mneuhaus/wonky/docs/native-bridge/proposal-resident.md

# Native bridge proposal: native-resident bodies behind a narrow session API

Date: 2026-09-22. Bend 2.0.25, Apple M5 Pro (18 logical CPUs), macOS arm64, Node v22.23.1.
Role: architecture proposal. It combines the four measurement reports in this folder
([profile](profile.md), [surface](surface.md), [binding](binding.md), [baseline](baseline.md)) with three small new
measurements (section 17). It builds no kernel and claims no speedup that was not measured. Every end-to-end number
below is an **arithmetic projection** from measured parts, generated by `scripts/native-bridge/resident-projection.mjs`.
All inputs were measured on a shared machine at load average 11.6 to 15.2 on 18 cores, so they are indicative.

## 0. Verdict

1. **In-process embedding works, so this design builds on it.** The binding stage ran Bend-emitted C inside Node as a
   plain N-API addon: 0.5 µs per empty call, bit-exact with the JS target, and as fast as a standalone native
   binary. It also proved **heap residency on the real kernel**: `subtract` kept its result in the Bend heap, that
   body fed `union` directly, and the result was bit-exact with the JS chain (`kernel-t1.json`, `chain`). The
   out-of-process service costs 22 to 29 µs per call and 26 ms per MB. It stays an optional isolation layer, not the
   binding.
2. **Residency is not a speed feature, and this proposal does not sell it as one.** The native chain and the same
   chain routed through JS differ by less than 1 % (1521 vs 1501 to 1513 ms). Marshaling costs under 1.5 ms per heavy
   operation. The speed comes from two other sources, and neither depends on residency:
   - native execution: k = 8.3 to 9.7 at 1 thread and 12.8 to 15.3 at 6 threads on the four measured planar Boolean
     calls;
   - not loading the Bend-compiled JS kernel: 745 to 806 ms per CLI run.
3. **What residency buys:**
   - **Exactness by construction.** `nativeChainExact: false` goes away because nothing is decoded and re-encoded
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
