mneuhaus/wonky/fixtures/fillet/onshape/fp22/fp22c.stl

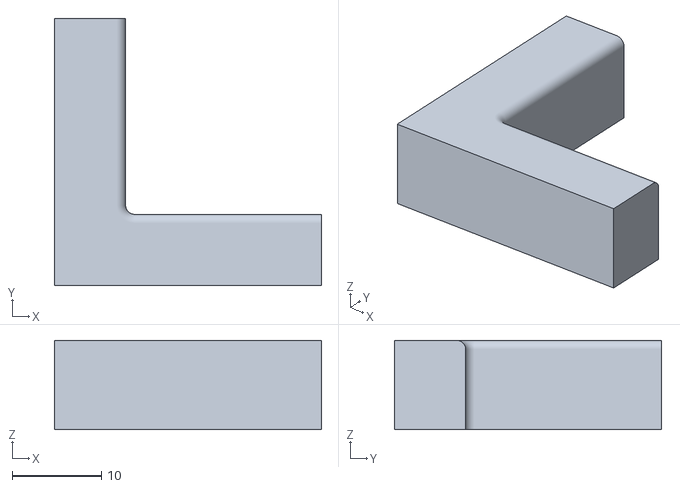
[picture p15: CAD file, 2026-09-27]
fixtures/fillet/onshape/fp22/fp22c.stl
30.0 x 30.0 x 10.0
