mneuhaus/wonky/fixtures/step-regression/periodic-pcurves/model.step

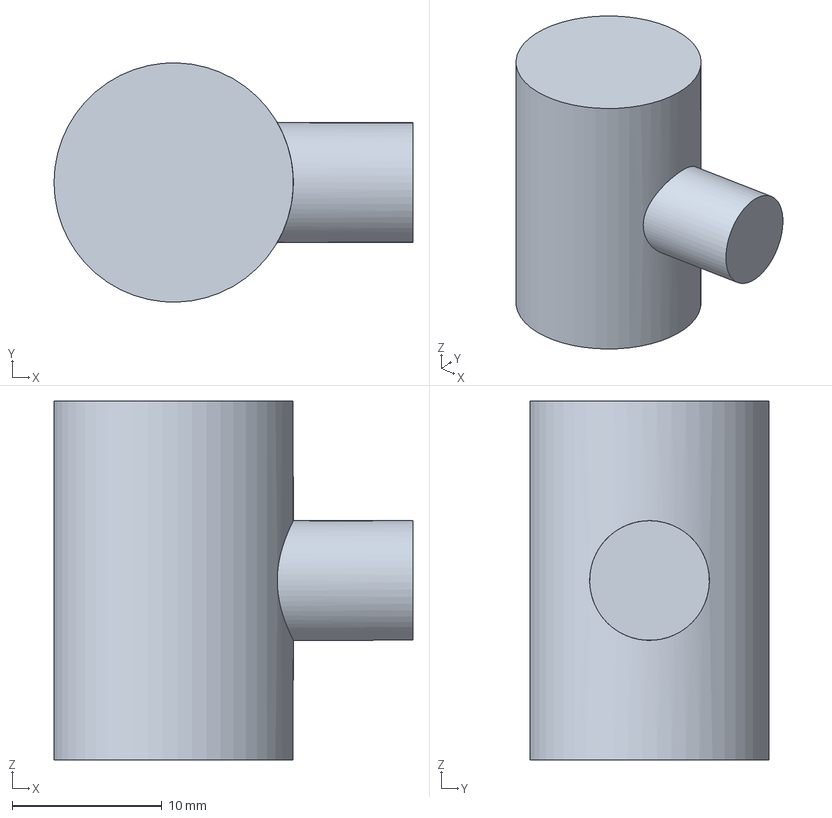
[picture p16: CAD file, 2026-10-04]
fixtures/step-regression/periodic-pcurves/model.step
24.0 x 16.0 x 24.0 mm
