mneuhaus/wonky/fixtures/fillet/onshape/fp17/fp17c.stl

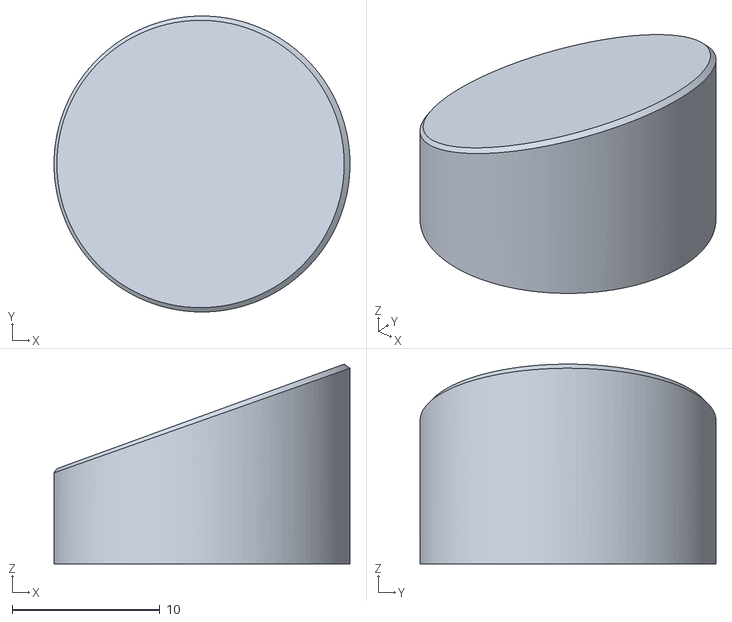
[picture p17: CAD file, 2026-09-27]
fixtures/fillet/onshape/fp17/fp17c.stl
20.0 x 20.0 x 13.5
