mneuhaus/wonky/fixtures/fillet/onshape/fp18/fp18c.stl

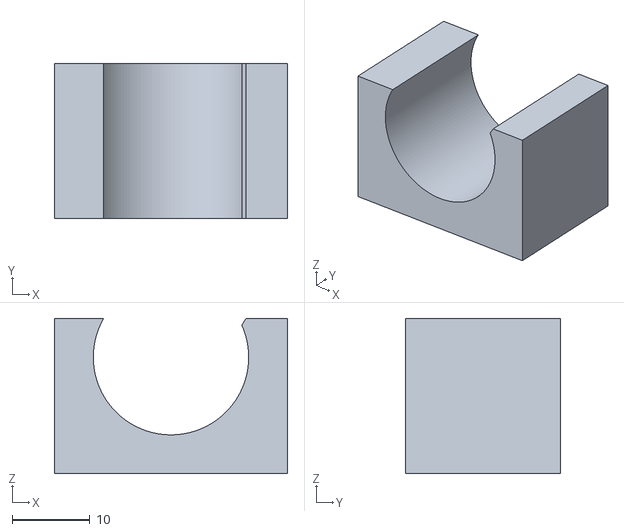
[picture p18: CAD file, 2026-09-27]
fixtures/fillet/onshape/fp18/fp18c.stl
30.0 x 20.0 x 20.0
