mneuhaus/wonky/fixtures/fillet/onshape/fp21/fp21a.stl

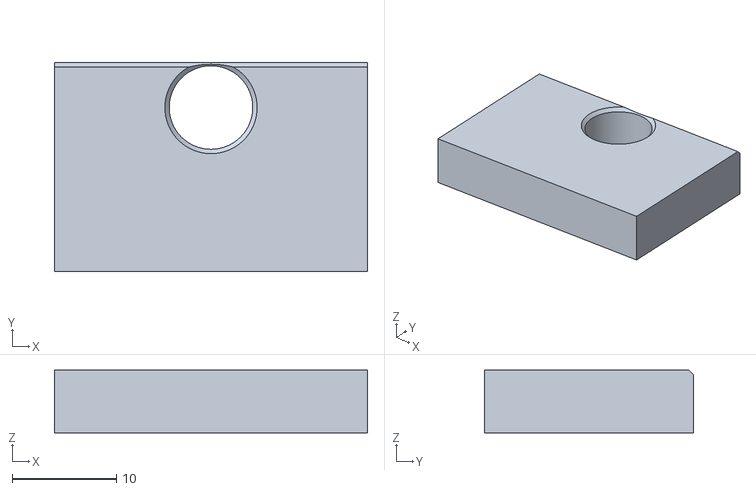
[picture p19: CAD file, 2026-09-27]
fixtures/fillet/onshape/fp21/fp21a.stl
30.0 x 20.0 x 6.00
