mneuhaus/wonky/fixtures/rust/occt-oracle/exports/boolean-overlap-union.step

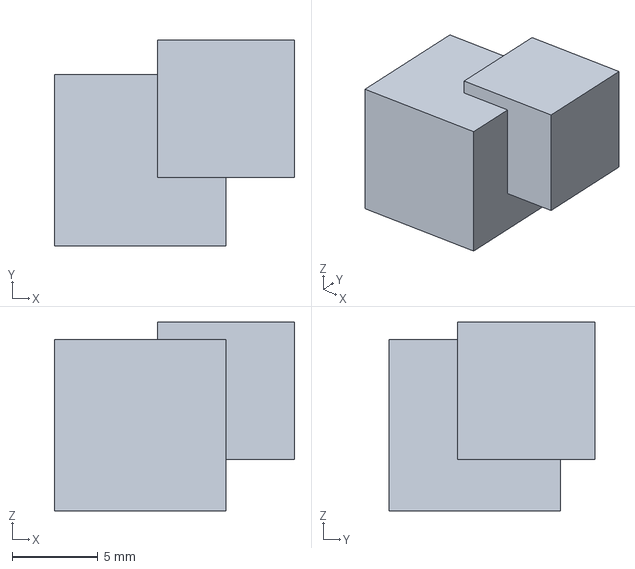
[picture p20: CAD file, 2026-09-27]
fixtures/rust/occt-oracle/exports/boolean-overlap-union.step
14.0 x 12.0 x 11.0 mm
