mneuhaus/wonky/fixtures/fillet/onshape/fp17/fp17b.stl

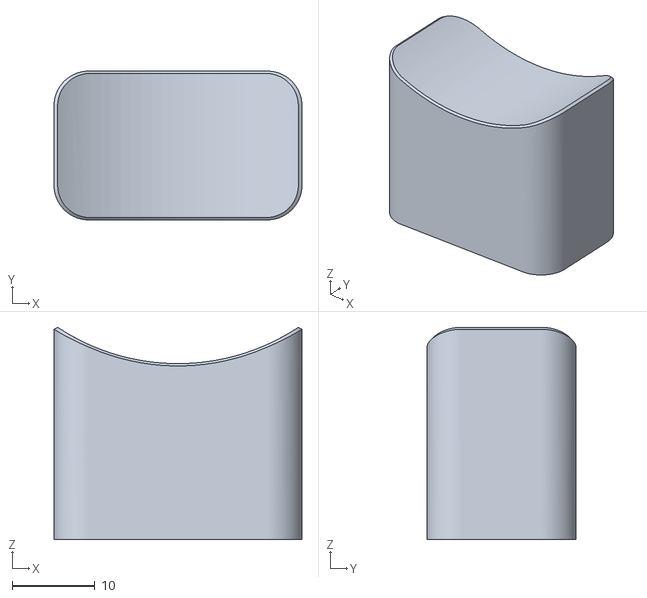
[picture p21: CAD file, 2026-09-27]
fixtures/fillet/onshape/fp17/fp17b.stl
30.0 x 18.0 x 25.7
