mneuhaus/wonky/fixtures/fillet/onshape/fp18/fp18a.stl

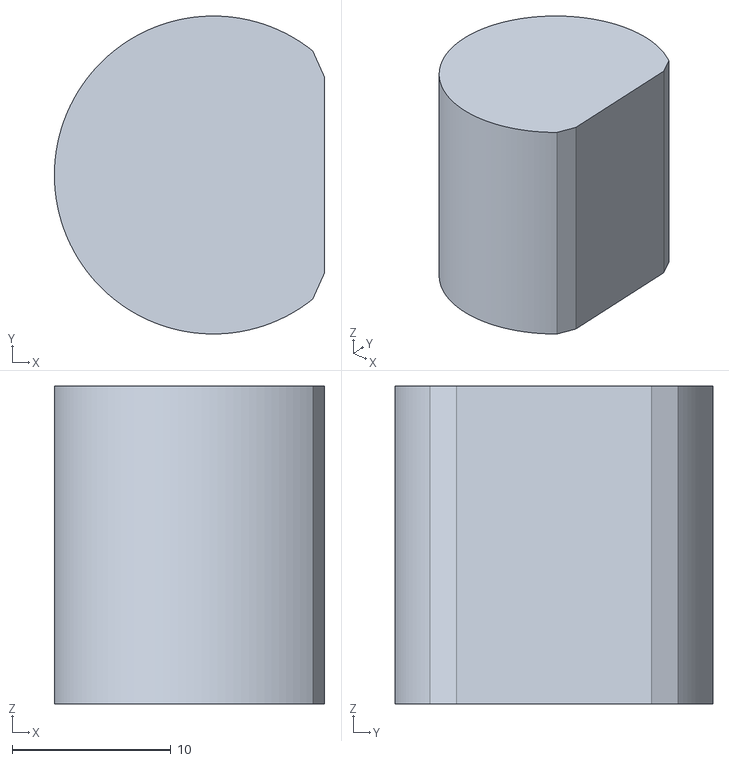
[picture p22: CAD file, 2026-09-27]
fixtures/fillet/onshape/fp18/fp18a.stl
17.0 x 20.0 x 20.0
