mneuhaus/wonky/fixtures/rust/occt-oracle/exports/boolean-sphere-near-tangent-contained-intersect.step

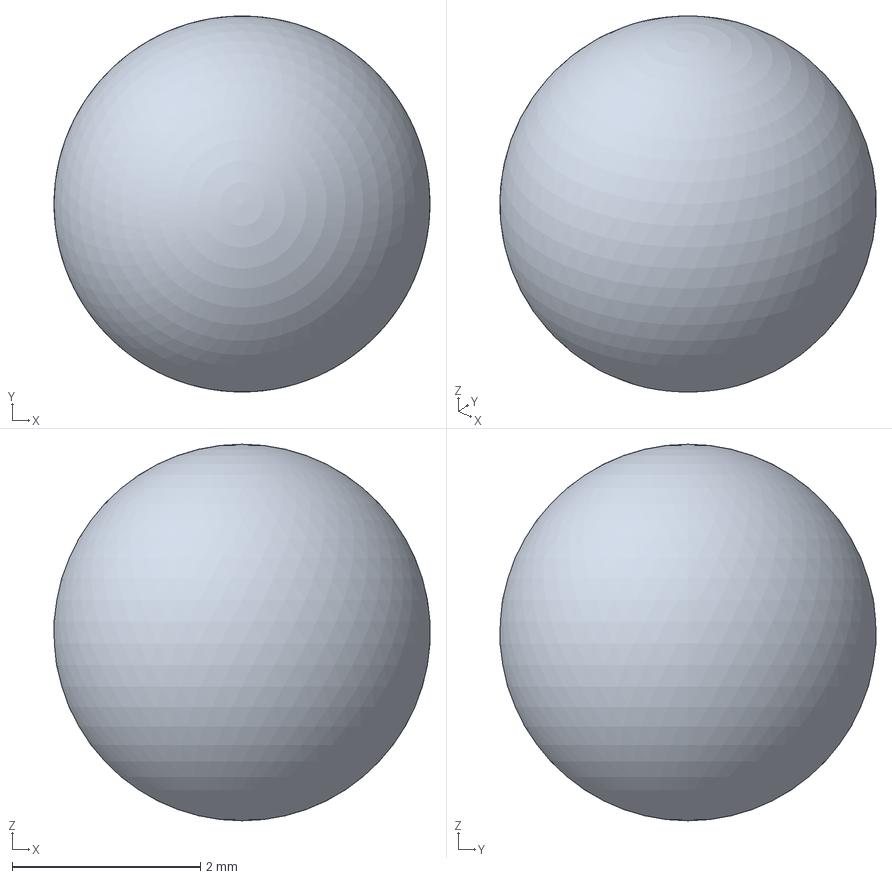
[picture p23: CAD file, 2026-09-27]
fixtures/rust/occt-oracle/exports/boolean-sphere-near-tangent-contained-intersect.step
3.99 x 3.99 x 4.00 mm
