mneuhaus/wonky/fixtures/rust/occt-oracle/exports/primitive-box.step

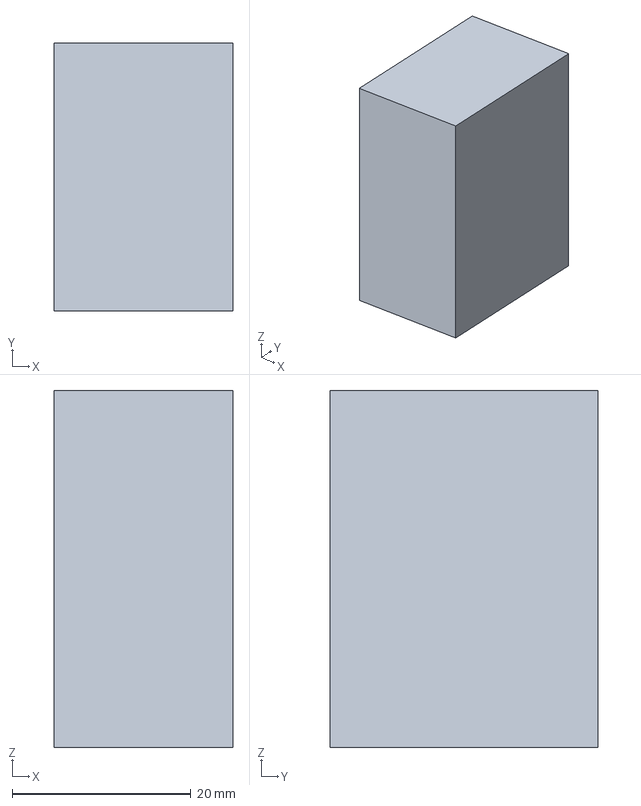
[picture p24: CAD file, 2026-09-27]
fixtures/rust/occt-oracle/exports/primitive-box.step
20.0 x 30.0 x 40.0 mm
