mneuhaus/wonky/fixtures/rust/occt-oracle/exports/boolean-sphere-internal-tangent-subtract.step

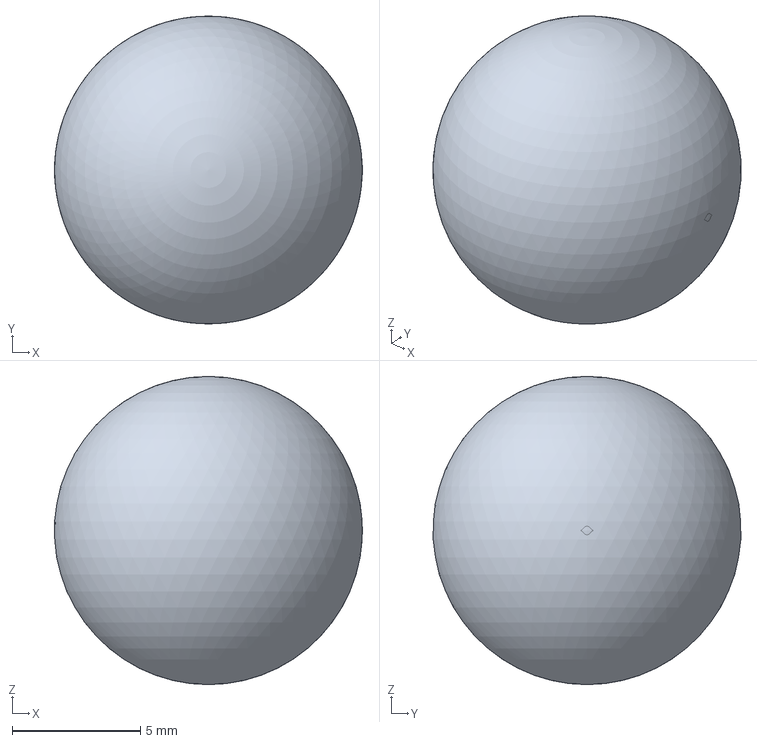
[picture p25: CAD file, 2026-09-27]
fixtures/rust/occt-oracle/exports/boolean-sphere-internal-tangent-subtract.step
12.0 x 12.0 x 12.0 mm
