mneuhaus/wonky/fixtures/rust/occt-oracle/exports/primitive-sphere.step

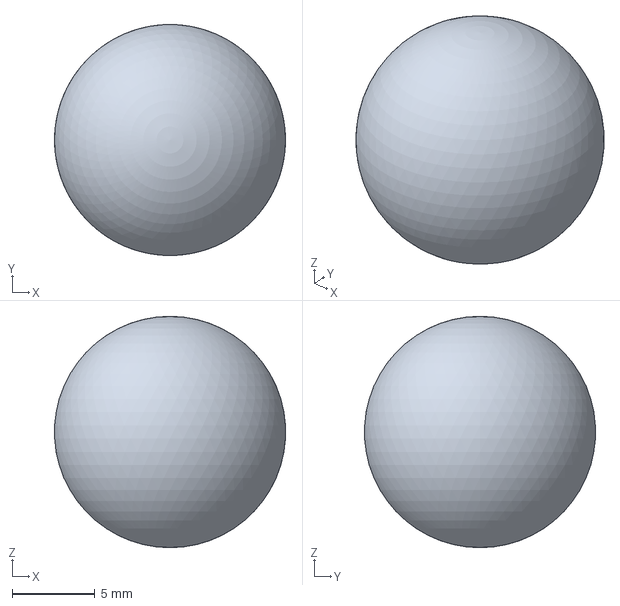
[picture p26: CAD file, 2026-09-27]
fixtures/rust/occt-oracle/exports/primitive-sphere.step
14.0 x 14.0 x 14.0 mm
