mneuhaus/wonky/fixtures/rust/occt-oracle/exports/primitive-cone.step

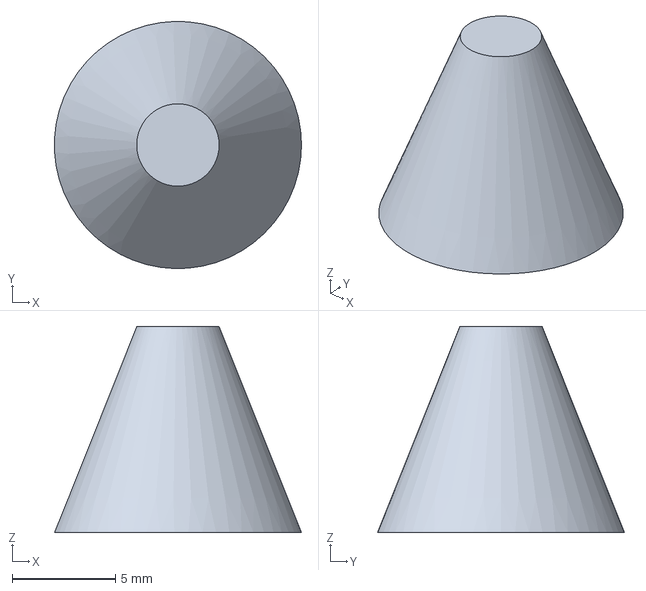
[picture p27: CAD file, 2026-09-27]
fixtures/rust/occt-oracle/exports/primitive-cone.step
12.0 x 12.0 x 10.0 mm
