mneuhaus/wonky/fixtures/rust/occt-oracle/exports/fillet-box-all-edges-r1_5.step

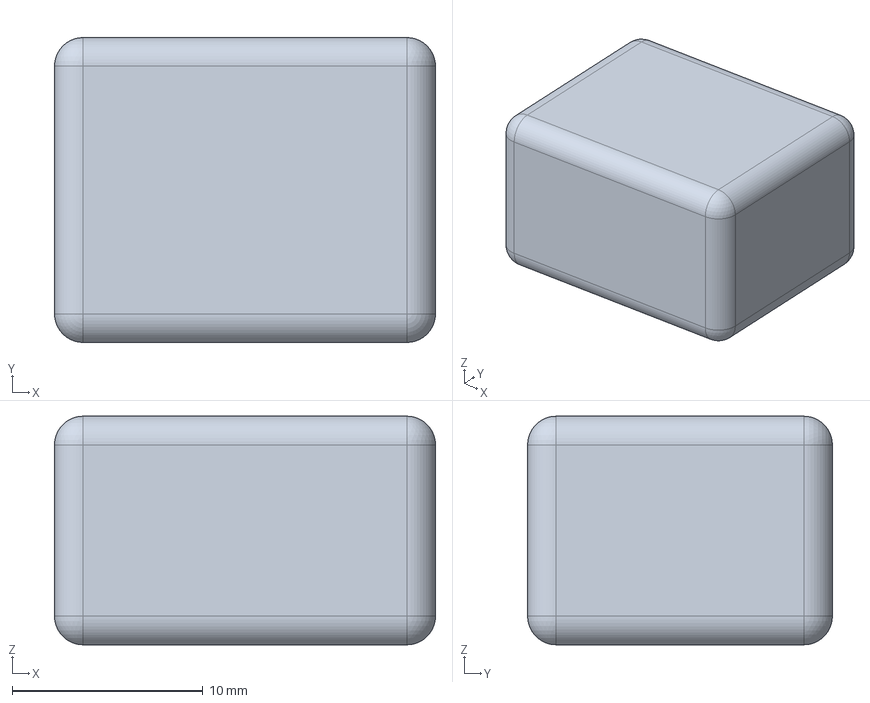
[picture p28: CAD file, 2026-09-27]
fixtures/rust/occt-oracle/exports/fillet-box-all-edges-r1_5.step
20.0 x 16.0 x 12.0 mm
