mneuhaus/wonky/fixtures/rust/occt-oracle/exports/boolean-overlap-subtract.step

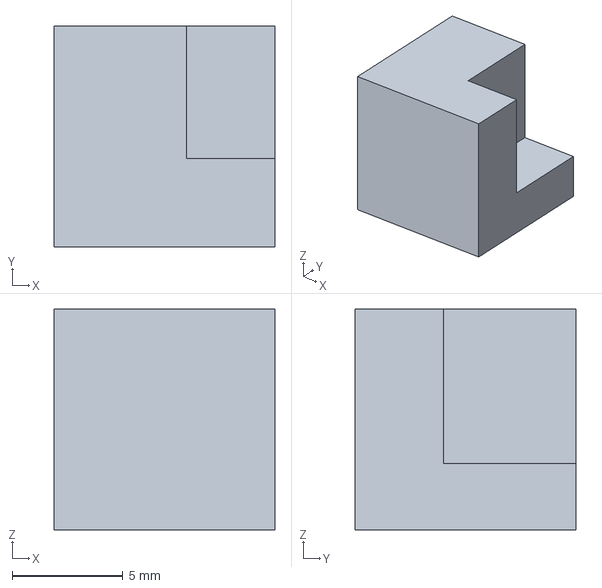
[picture p29: CAD file, 2026-09-27]
fixtures/rust/occt-oracle/exports/boolean-overlap-subtract.step
10.0 x 10.0 x 10.0 mm
