mneuhaus/wonky/fixtures/rust/occt-oracle/exports/boolean-coplanar-coincident-faces-union.step

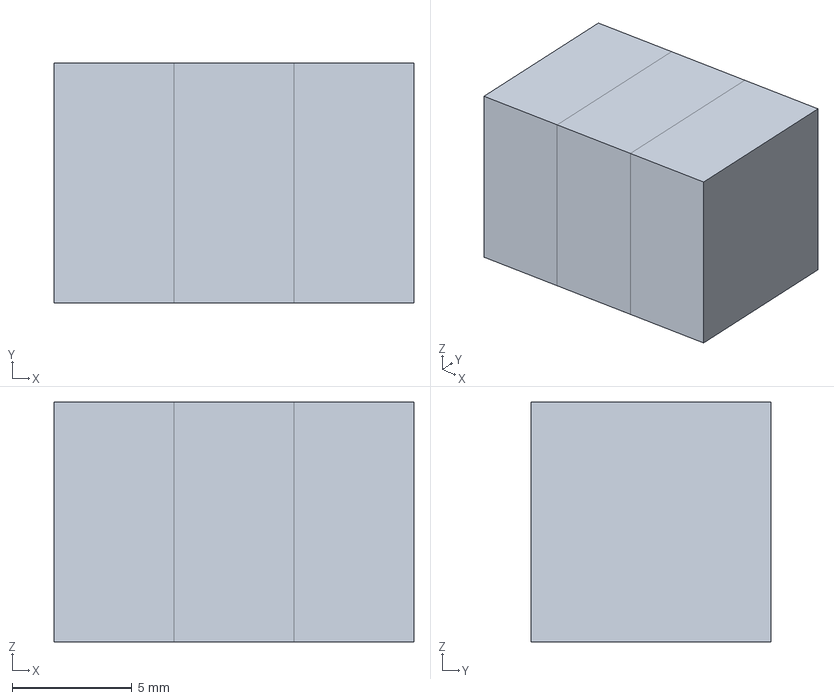
[picture p30: CAD file, 2026-09-27]
fixtures/rust/occt-oracle/exports/boolean-coplanar-coincident-faces-union.step
15.0 x 10.0 x 10.0 mm
