mneuhaus/wonky/fixtures/rust/occt-oracle/exports/boolean-overlap-intersect.step

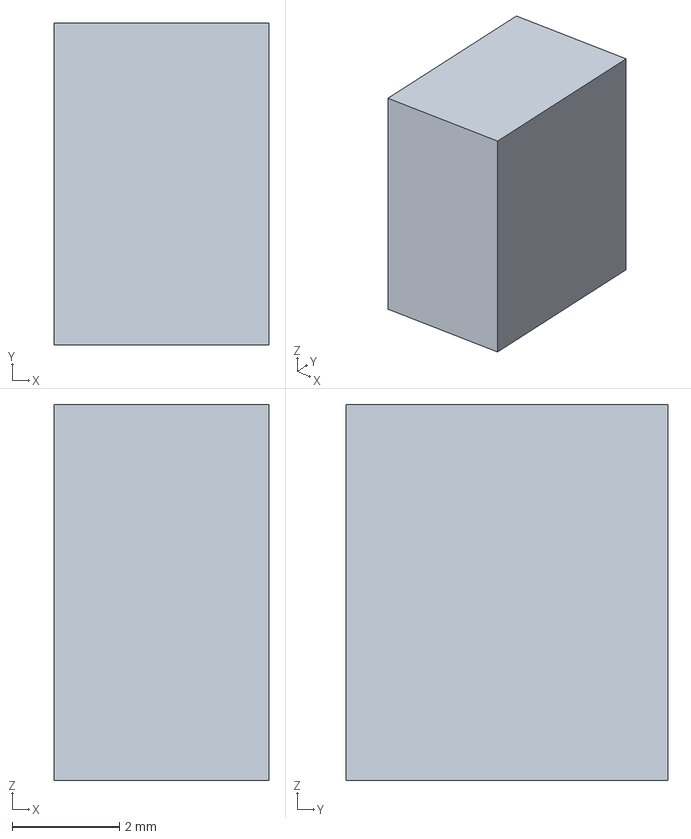
[picture p31: CAD file, 2026-09-27]
fixtures/rust/occt-oracle/exports/boolean-overlap-intersect.step
4.00 x 6.00 x 7.00 mm
