mneuhaus/wonky/fixtures/rust/occt-oracle/exports/boolean-coplanar-coincident-faces-subtract.step

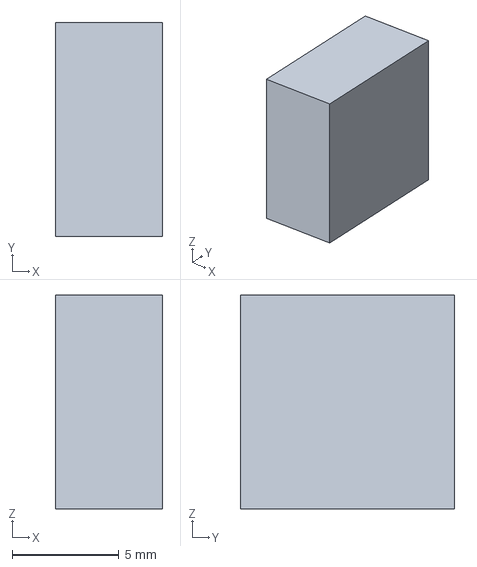
[picture p33: CAD file, 2026-09-27]
fixtures/rust/occt-oracle/exports/boolean-coplanar-coincident-faces-subtract.step
5.00 x 10.0 x 10.0 mm
