mneuhaus/wonky/fixtures/rust/occt-oracle/exports/primitive-cylinder.step

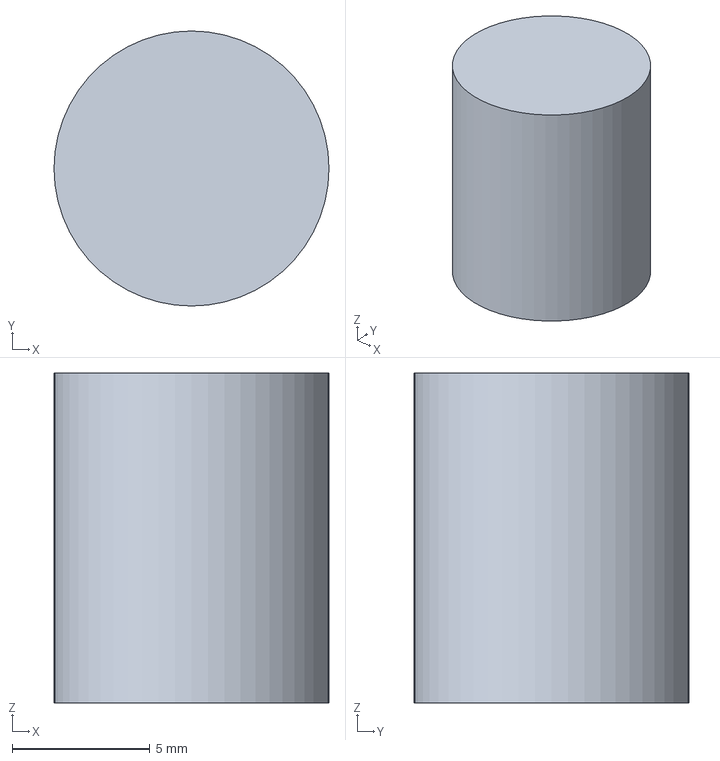
[picture p34: CAD file, 2026-09-27]
fixtures/rust/occt-oracle/exports/primitive-cylinder.step
10.0 x 10.0 x 12.0 mm
