mneuhaus/wonky/fixtures/rust/occt-oracle/exports/fillet-plate-vertical-edges-r1_5.step

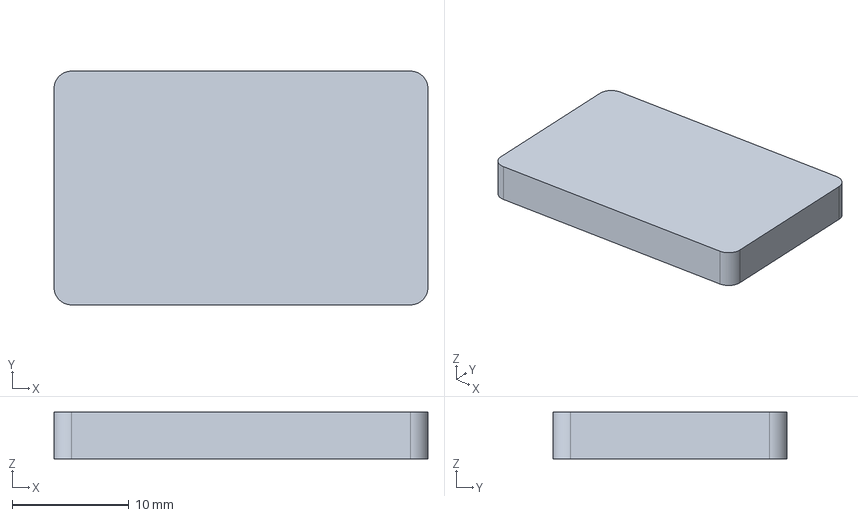
[picture p35: CAD file, 2026-09-27]
fixtures/rust/occt-oracle/exports/fillet-plate-vertical-edges-r1_5.step
32.0 x 20.0 x 4.00 mm
