mneuhaus/wonky/fixtures/rust/occt-oracle/exports/primitive-prism.step

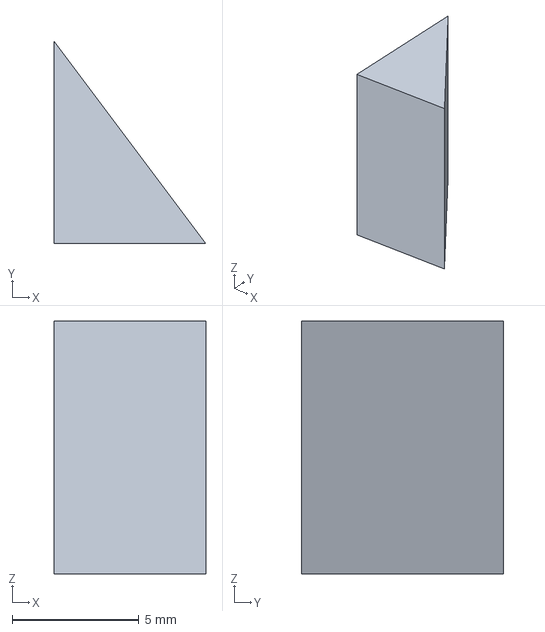
[picture p36: CAD file, 2026-09-27]
fixtures/rust/occt-oracle/exports/primitive-prism.step
6.00 x 8.00 x 10.0 mm
