mneuhaus/wonky/docs/research/sources/open-boolean-benchmark-boolean-benchmark-runners.md

# Open Boolean Benchmark: boolean-benchmark-runners

- Kind: open-source benchmark harness (runner adapters plus JSON I/O contract), code repository.
- Canonical URL: https://github.com/Open-Boolean-Benchmark/boolean-benchmark-runners
- Other URLs: benchmark data https://github.com/solidean/bench-blog-data (MIT code, CC BY 4.0 meshes); result write-ups https://solidean.com/blog/2026/first-benchmark-results-iterated-csg/, https://solidean.com/blog/2026/iterated-cube-grid-benchmark/, https://solidean.com/blog/2026/terrain-carve-benchmark/, https://solidean.com/blog/2026/iterated-dome-carve-benchmark/.
- Authors/organization, year: GitHub org "Open-Boolean-Benchmark"; all 27 commits by Philip-Trettner (EMBER first author, Solidean/Shaped Code). Created 2026-03-29. DOCUMENTED (`gh api repos/Open-Boolean-Benchmark/boolean-benchmark-runners/contributors`, 2026-09-22).
- License: MIT for the harness. Each wrapped library keeps its own licence (GPL for CGAL, Carve, Blender, Mesh Arrangements; non-commercial for Solidean, Trueform, MeshLib, QuickCSG; BSD-3 for Geogram and VTK; MIT for IARMB; Apache-2.0 for Manifold). `build-all.py -y` means accepting all of them. DOCUMENTED (README, https://github.com/Open-Boolean-Benchmark/boolean-benchmark-runners/blob/main/README.md). Porting implication: the harness, protocol and smoke test are freely reusable; do not vendor the wrapped libraries into wonky.
- Status: 8 stars, 3 forks, 0 open issues, 0 issues ever filed, last commit a41f0d6 "added bbox check for smoke test" on 2026-06-08. Single maintainer. The meta-runner (case planner, correctness evaluation, aggregation) is referenced by the docs but not in this repo. INFERRED: meta-runner not yet published (the first benchmark post says "the runner programs that wrap each implementation are already open source", https://solidean.com/blog/2026/first-benchmark-results-iterated-csg/). DOCUMENTED for the metadata (`gh api`, 2026-09-22). Re-checked 2026-09-24: 9 stars, HEAD still a41f0d6, still 0 issues ever filed. No commit in 3.5 months while Solidean's own benchmark posts also stopped after 2026-07-02, so the project is dormant rather than active. DOCUMENTED (`gh api`, https://solidean.com/blog/); "dormant" INFERRED.
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
