mneuhaus/wonky/rust/wonky-curve/src/witness.rs

//! A strict interior witness of an arrangement cell: an exact point that
//! lies inside the cell and on none of its boundary pieces.
//!
//! Construction (rational proposals with exact certification): `m` is the interior point of the first
//! piece of the cell's outer cycle. The cell lies on the left of every
//! half-edge of its cycles, so a ray from `m` along the coordinate axis
//! direction that is strictly to the left of the piece's tangent at `m`
//! enters the cell. The probe is that ray up to an exact far point beyond
//! every piece. The witness is the midpoint of `m` and the nearest point
//! where the probe meets a piece of the cell or one of the caller's
//! obstacles (other than `m` itself). The open segment between them meets no
//! piece of the cell, so the midpoint lies strictly inside it: pieces on the
//! probe's own line count with their ends, and a run of such pieces is
//! entered through a non-collinear piece at the run's nearer end.
//!
//! The consumer re-checks the witness exactly (winding and containment);
//! this construction only has to find one.
use crate::arrangement::Arrangement;
use crate::carrier::Carrier;
use crate::numeric::{q, P, Q};
use crate::point::ExactPoint;
use crate::refusal::{Refusal, R};
use crate::trimmed::Trimmed;
use num_traits::Zero;
use wonky_num::Scalar;

/// An exact bound of `|x_k - from|` over every point of the piece. A spline
/// piece refuses like every other arrangement operation on it (S6).
fn reach(piece: &Trimmed, k: usize, from: &Q) -> R<Q> {
    let end = |p: &ExactPoint| -> R<Q> { Ok(q((p.coordinates()[k].clone() - from).enclosure()?.abs().hi())) };
    let ends = end(&piece.ends()[0])?.max(end(&piece.ends()[1])?);
    match piece.carrier() {
        Carrier::Line => Ok(ends),
        // |x_k - c_k| <= r <= r2 + 1 anywhere on the circle.
        Carrier::Circle(c) => Ok(ends.max(q((c.c.coordinates()[k].clone() - from).enclosure()?.abs().hi()) + q(c.r2.enclosure()?.hi()) + q(1.))),
        Carrier::BSpline(_) => Err(Refusal::SplineArrangement),
    }
}

/// A rational within `width` of an exact coordinate. Initial observation
/// enclosures only propose a bracket; all refinement and acceptance are exact.
fn rational_near(x: &crate::radical::Radical, width: &Q) -> R<Q> {
    if let Some(q) = x.rational() {return Ok(q);}
    let iv = x.enclosure()?;
    let (mut lo, mut hi) = (q(iv.lo()), q(iv.hi()));
    for _ in 0..2048 {
        let middle = (&lo + &hi) / q(2.);
        if &hi - &lo <= *width {return Ok(middle);}
        match x.cmp(&crate::radical::Radical::from(middle.clone())) {
            std::cmp::Ordering::Less => hi = middle,
            std::cmp::Ordering::Greater => lo = middle,
            std::cmp::Ordering::Equal => return Ok(middle),
        }
    }
    Err(Refusal::RadicalBudget)
}

impl Arrangement {
    /// Quadratic boundary points need not have a rational point on the
    /// boundary itself. Propose rational points in its inward neighbourhood,
    /// then certify strict cell winding and absence of every obstacle. The
    /// coordinate error shrinks quadratically with the inward step; nothing
    /// accepts a point merely because it is close to the boundary.
    fn quadratic_witness(&self, cell: usize, m: &ExactPoint, k: usize, sign: &Q,
        pieces: &[Trimmed], points: &[ExactPoint]) -> R<ExactPoint> {
        crate::radical::guard(|| {
            let cycles: Vec<_> = self.cells[cell].cycles.iter().map(|c|self.cycle_profile(c)).collect();
            let own: Vec<_> = self.cells[cell].cycles.iter().flatten().map(|&h|&self.pieces[h/2].seg).collect();
            // Preserve the obstacle capability contract before any proposal.
            for piece in pieces {match piece.carrier() {
                Carrier::Line|Carrier::Circle(_) => {},
                Carrier::BSpline(_) => return Err(Refusal::SplineArrangement),
            }}
            let coordinates = m.coordinates();
            let mut delta = q(1.);
            for _ in 0..512 {
                let accuracy = &delta * &delta / q(16.);
                let mut p = [rational_near(&coordinates[0], &accuracy)?, rational_near(&coordinates[1], &accuracy)?];
                p[k] += sign * &delta;
                let p = ExactPoint::from_rational(p);
                let mut on = points.contains(&p);
                for piece in own.iter().copied().chain(pieces) {
                    if piece.contains(&p)? {on=true;break;}
                }
                if !on {
                    let mut winding = 0;
                    for cycle in &cycles {winding += cycle.winding(&p)?;}
                    if winding == 1 {return Ok(p);}
                }
                delta /= q(2.);
            }
            Err(Refusal::RadicalBudget)
        })?
    }
    /// An exact point strictly inside bounded cell `cell`, also off the
    /// caller's `pieces` and `points` (features inside the cell that must be
    /// avoided, such as pieces that split nothing and isolated contacts).
    /// Quadratic crossings bound the exact open witness interval; a rational
    /// proposal is then checked against that interval without rounded order.
    pub fn witness(&self, cell: usize, pieces: &[Trimmed], points: &[ExactPoint]) -> R<ExactPoint> {
        self.witness_impl(cell, pieces, points, false)
    }
    /// Exact rational interior proposals also for cells bounded by quadratic
    /// lines. Dark arithmetic admission: existing callers retain `witness`;
    /// G10 uses this method without changing any public geometry route.
    pub fn witness_exact(&self, cell: usize, pieces: &[Trimmed], points: &[ExactPoint]) -> R<ExactPoint> {
        self.witness_impl(cell, pieces, points, true)
    }
    fn witness_impl(&self, cell: usize, pieces: &[Trimmed], points: &[ExactPoint], quadratic: bool) -> R<ExactPoint> {
        let cycles = &self.cells[cell].cycles;
        let first = self.oriented(cycles[0][0]);
        let m = if quadratic { first.exact_interior_point()? } else { first.interior_point()? };
        // Tangent at m along the half-edge, from the sub-piece that starts at m.
        let tangent = first.trim(m.clone(), first.ends()[1].clone())?.tangent(true).0;
        // The axis direction strictly to the left of the tangent: (k, sign).
        let (k, sign): (usize, Q) = if tangent[0].is_positive() {
            (1, q(1.))
        } else if tangent[0].is_negative() {
            (1, q(-1.))
        } else if tangent[1].is_positive() {
            (0, q(-1.))
        } else {
            (0, q(1.))
        };
        let mut unit: P = [Q::zero(), Q::zero()];
        unit[k] = sign.clone();
        debug_assert!(crate::radical::cross(&tangent, &crate::radical::vector(&unit)).is_positive());
        match &m {
            ExactPoint::Rational(_) => {},
            ExactPoint::Quadratic(_) | ExactPoint::Algebraic(_) | ExactPoint::Real(_) => return self.quadratic_witness(cell, &m, k, &sign, pieces, points),
        }
        let own = cycles.iter().flatten().map(|&h| &self.pieces[h / 2].seg).collect::<Vec<_>>();
        let from = &m.rat()?[k];
        let mut far = q(1.);
        for s in own.iter().copied().chain(pieces) {
            far = far.max(reach(s, k, from)? + q(1.));
        }
        for p in points {
            far = far.max(q((p.coordinates()[k].clone() - from).enclosure()?.abs().hi()) + q(1.));
        }
        let mut end = m.rat()?.clone();
        end[k] = &end[k] + &sign * &far;
        let probe = Trimmed::new([m.clone(), ExactPoint::from_rational(end)], Carrier::Line)?;
        let mut hits = vec![];
        for s in own.iter().copied().chain(pieces) {
            if s.coincident_with(&probe)? {
                for e in s.ends() { if probe.contains(e)? { hits.push(e.clone()); } }
            } else {
                hits.extend(s.contacts(&probe)?);
            }
        }
        for p in points { if probe.contains(p)? { hits.push(p.clone()); } }
        hits.retain(|p| *p != m);
        // A probe from inside the cell's outer cycle to beyond every piece
        // leaves that cycle again; no hit means the cycle is not closed.
        let nearest = probe.sorted_cuts(hits)?.into_iter().next().ok_or(Refusal::FaceWalk)?;
        let (a, b) = (m.coordinates(), nearest.coordinates());
        let middle = (&a[k] + &b[k]) / q(2.);
        let mut p = m.rat()?.clone();
        // Rational cells need no export-resolution admission here: a strict
        // witness may lie between adjacent binary64 values. Only a genuinely
        // irrational midpoint needs a rounded proposal and exact certification.
        p[k] = match middle.rational() {
            Some(value) => value,
            None => q(middle.enclosure()?.m),
        };
        let p = ExactPoint::from_rational(p);
        if p == m || p == nearest || !probe.trim(m.clone(), nearest.clone())?.contains(&p)? { return Err(Refusal::SubResolutionFeature); }
        Ok(p)
    }
}
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
