mneuhaus/wonky/rust/wonky-ops/src/analytic.rs

//! Dispatch by audited analytic carrier, never by caller-provided geometry tags.
use crate::{
    affine::Affine,
    cylinder::{self, Cylinder},
    polyhedron::{self, Audited, Refused},
};
use wonky_contract::{Body, BodyKey, CheckedBody};

type R<T> = Result<T, Refused>;
#[derive(Clone, Debug)]
pub enum Solid {
    Columns(crate::prism_columns::Columns),
    PrismHoles(crate::prism_holes::PrismHoles),
    PrismStack(crate::prism_stack::PrismStack),
    Revolved(crate::revolve_full::FullRevolve),
    Planar(Audited),
    /// Replayed rule-6 Model and its exact planar consumer view.
    Model(Audited, wonky_geom::model::Model),
    /// A placed body whose family owns no placement: Model consumers only.
    Placed(crate::model_curved::Placed),
    Cylinder(Cylinder),
    Conical(crate::chamfer_rim::Conical),
    Coaxial(crate::coaxial::Coaxial),
    Bicylinder(crate::bicylinder::Bicylinder),
    CylinderTee(crate::cylinder_tee::Tee),
    Spherical(crate::sphere::Spherical),
    Axial(crate::axial::Axial),
    Lens(crate::lens::Lens),
    Perforated(crate::perforated::Perforated),
    PerforatedChamfer(crate::perforated_chamfer::PerforatedChamfer),
}
pub fn audit(body: &CheckedBody) -> R<Solid> {
    // Rule-6 ownership precedes source-placement and family dispatch, even
    // when the replayed Model has the boundary of a primitive box.
    if crate::model_boolean::candidate(body.body()) && !cfg!(feature = "plant_model_shape_dispatch") {
        return crate::model_boolean::audit(body).map(|(a, m)| Solid::Model(a, m));
    }
    // Placement preserves the authenticated source carrier. A profile blend
    // contains cylinders but is still a planar-profile solid, not a cylinder.
    if let Some((inner, _)) = crate::pattern::unplace(body.body()) {
        let checked = inner.check().map_err(|_| Refused("audit/placed-source-contract".into()))?;
        match audit(&checked)? {
            Solid::Planar(_) => return polyhedron::audit(body).map(Solid::Planar),
            // Families without a placement owner keep their source and are
            // read through the exactly moved source Model.
            source @ (Solid::Revolved(_) | Solid::Placed(_)) =>
                return crate::model_curved::placed(body.body(), source).map(Solid::Placed),
            _ => {}
        }
    }
    // Source-profile placements retain their analytic carrier payload.
    if let Some(placed) = polyhedron::placed_source(body)? {
        return Ok(Solid::Planar(placed));
    }
    if crate::fillet_general::candidate(body.body()) {
        crate::fillet_general::audit(body).map(Solid::Planar)
    } else if crate::profile_blend::candidate(body.body()) {
        crate::profile_blend::audit(body).map(Solid::Planar)
    } else if crate::cylinder_tee::is_candidate(body.body()) {
        crate::cylinder_tee::audit(body).map(Solid::CylinderTee)
    } else if crate::prism_stack::candidate(body.body()) {
        crate::prism_stack::audit(body).map(Solid::PrismStack)
    } else if crate::perforated_chamfer::candidate(body.body()) {
        crate::perforated_chamfer::audit(body).map(Solid::PerforatedChamfer)
    } else if crate::prism_columns::candidate(body.body()) {
        crate::prism_columns::audit(body).map(Solid::Columns)
    } else if crate::prism_holes::candidate(body.body()) {
        crate::prism_holes::audit(body).map(Solid::PrismHoles)
    } else if crate::revolve_full::candidate(body.body()) {
        crate::revolve_full::audit(body).map(Solid::Revolved)
    } else if crate::arc_profile::candidate(body.body()) {
        polyhedron::audit(body).map(Solid::Planar)
    } else if crate::chamfer_rim::candidate(body.body()) {
        crate::chamfer_rim::audit(body).map(Solid::Conical)
    } else if crate::bicylinder::is_candidate(body.body()) {
        crate::bicylinder::audit(body).map(Solid::Bicylinder)
    } else if body.body().curves.iter().any(|c| matches!(c.geometry, wonky_contract::CurveGeometry::SphereCircle { .. })) {
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
